DamianAPaul/726-DSSI/726-DSSI_Images/Back.png

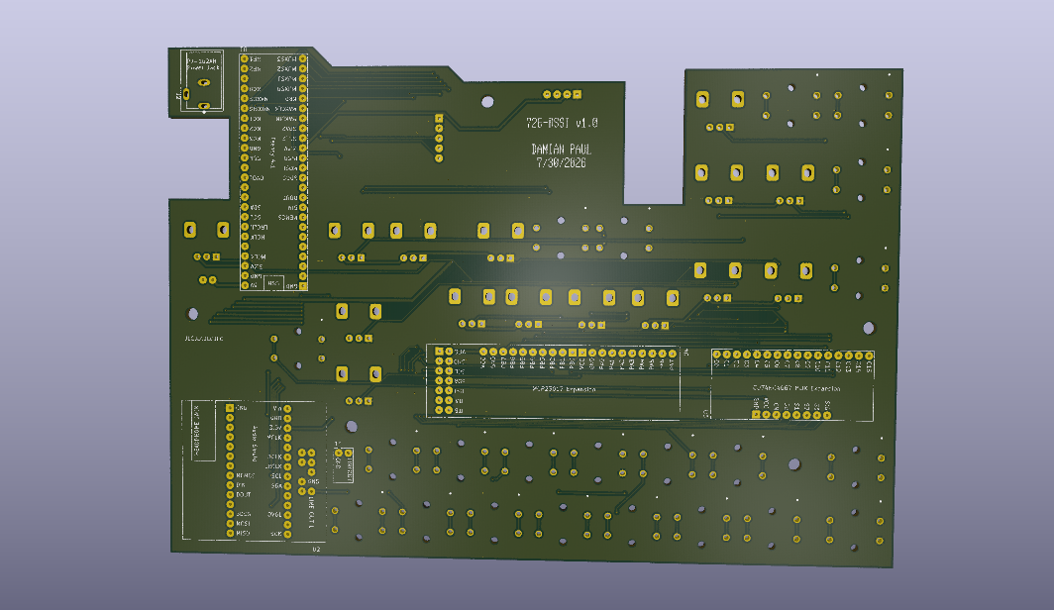
726-DSSI_Images/Back.png
