DamianAPaul/726-DSSI/726-DSSI_Images/Front.png

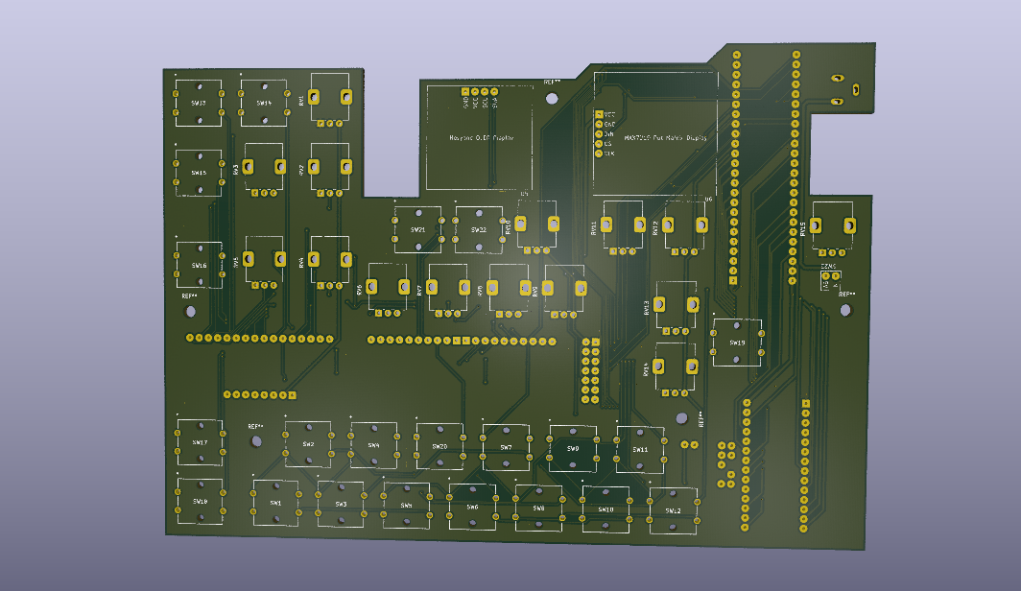
726-DSSI_Images/Front.png
