DamianAPaul/726-DSSI/726-DSSI_Images/IMG_2033_7_15_26.jpeg

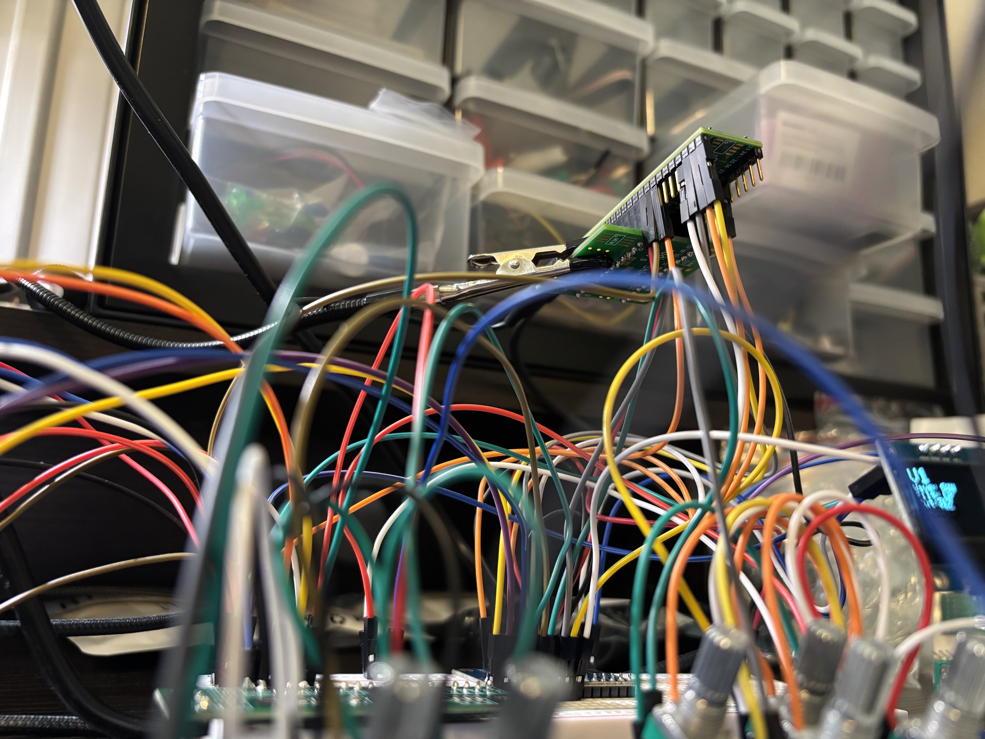
726-DSSI_Images/IMG_2033_7_15_26.jpeg
