DamianAPaul/726-DSSI/726-DSSI_Images/IMG_2102_7_22_26.jpeg

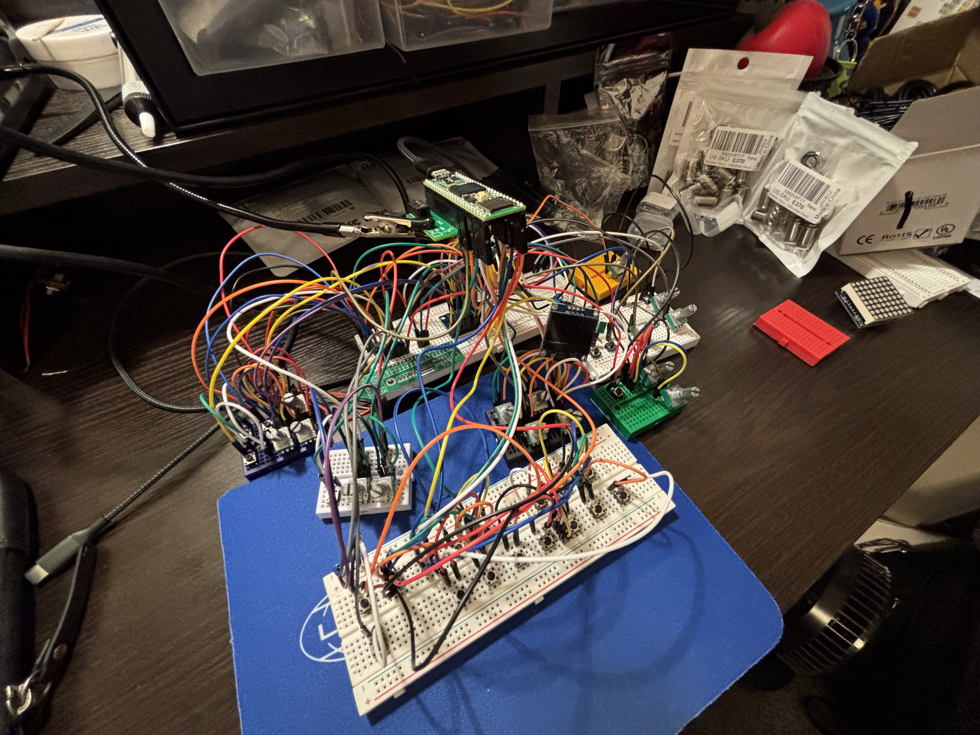
726-DSSI_Images/IMG_2102_7_22_26.jpeg
