DamianAPaul/726-DSSI/726-DSSI_Images/Screenshot 2026-07-22 at 4.46.47 PM.png

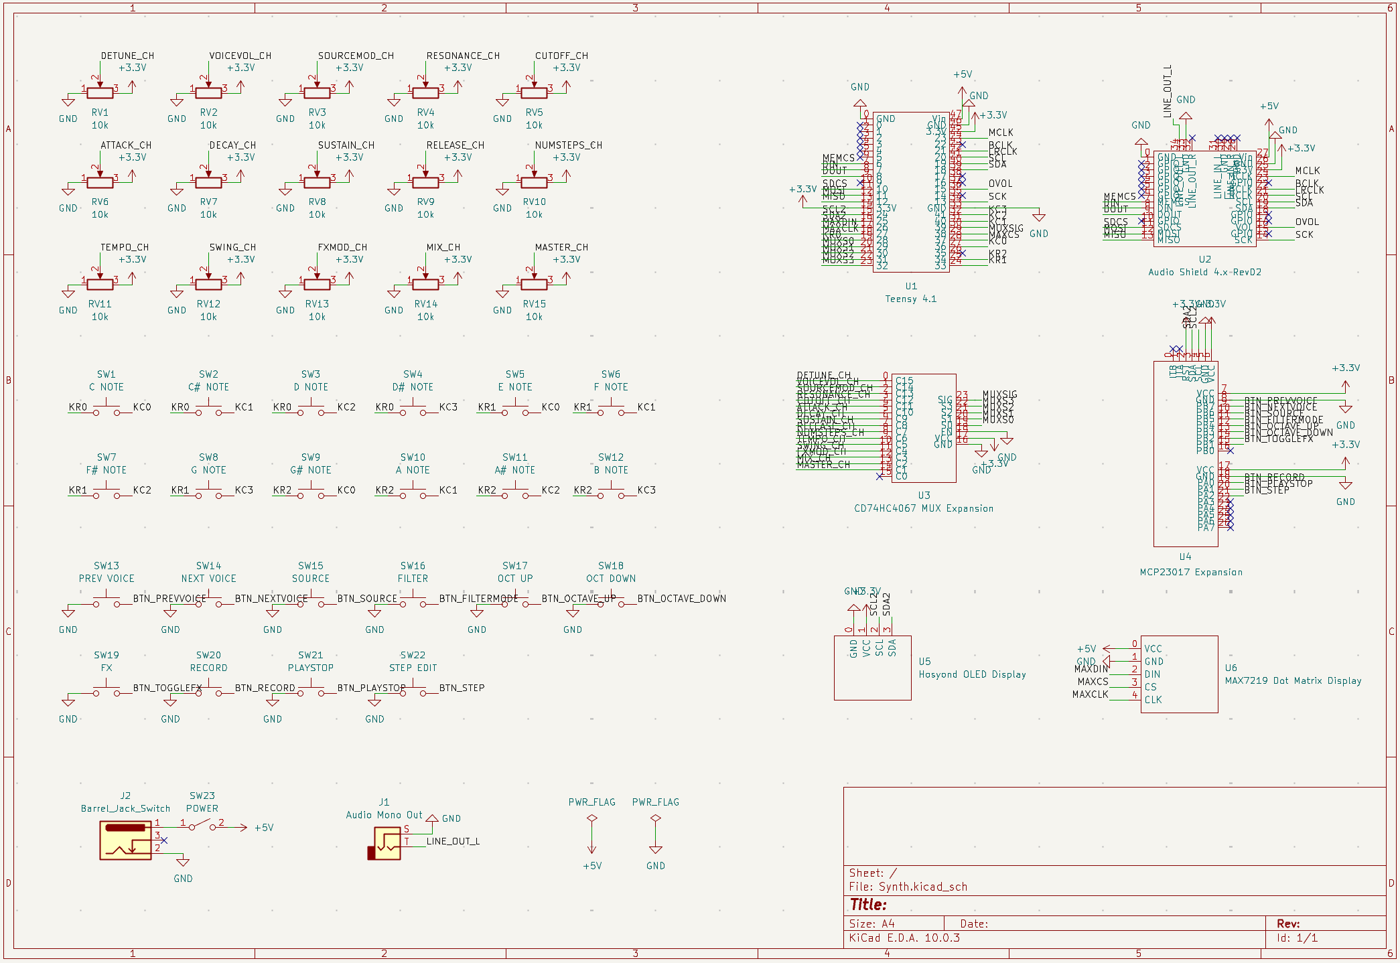
726-DSSI_Images/Screenshot 2026-07-22 at 4.46.47 PM.png
