DamianAPaul/726-DSSI/726-DSSI_Images/Screenshot 2026-07-30 at 5.10.47 PM.png

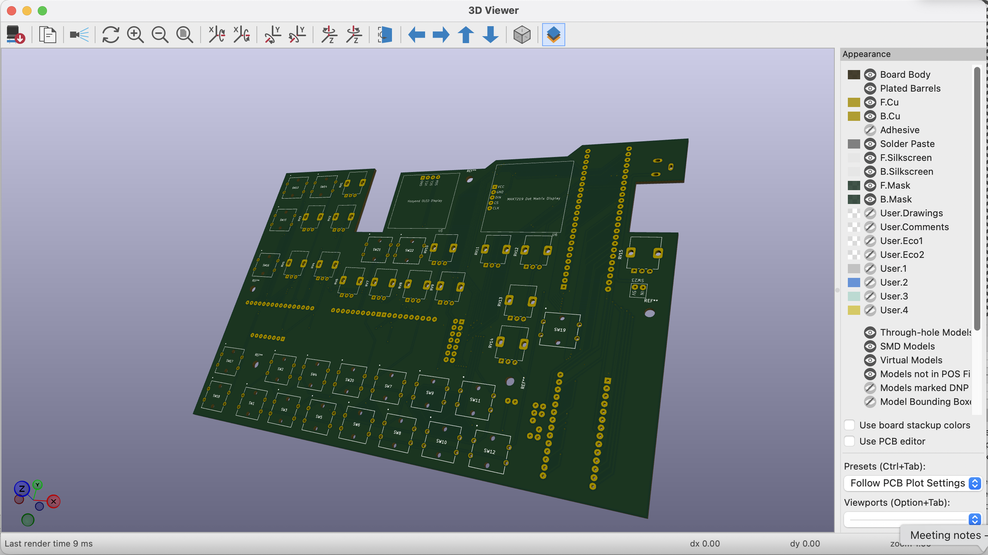
726-DSSI_Images/Screenshot 2026-07-30 at 5.10.47 PM.png
