DamianAPaul/726-DSSI/726-DSSI_Images/Screenshot 2026-07-30 at 12.36.37 PM.png

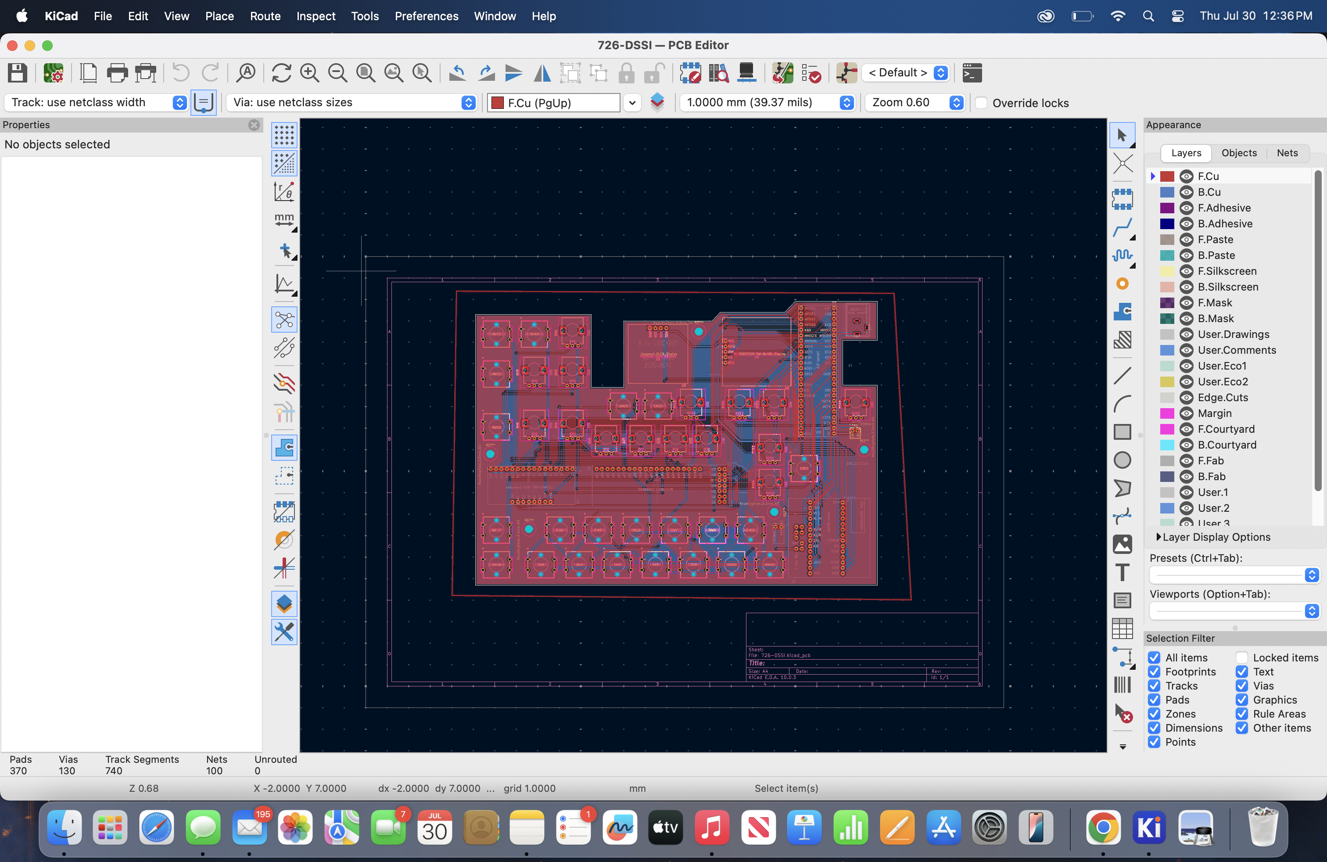
726-DSSI_Images/Screenshot 2026-07-30 at 12.36.37 PM.png
