DamianAPaul/726-DSSI/726-DSSI_Images/Screenshot 2026-08-05 at 1.29.30 PM.png

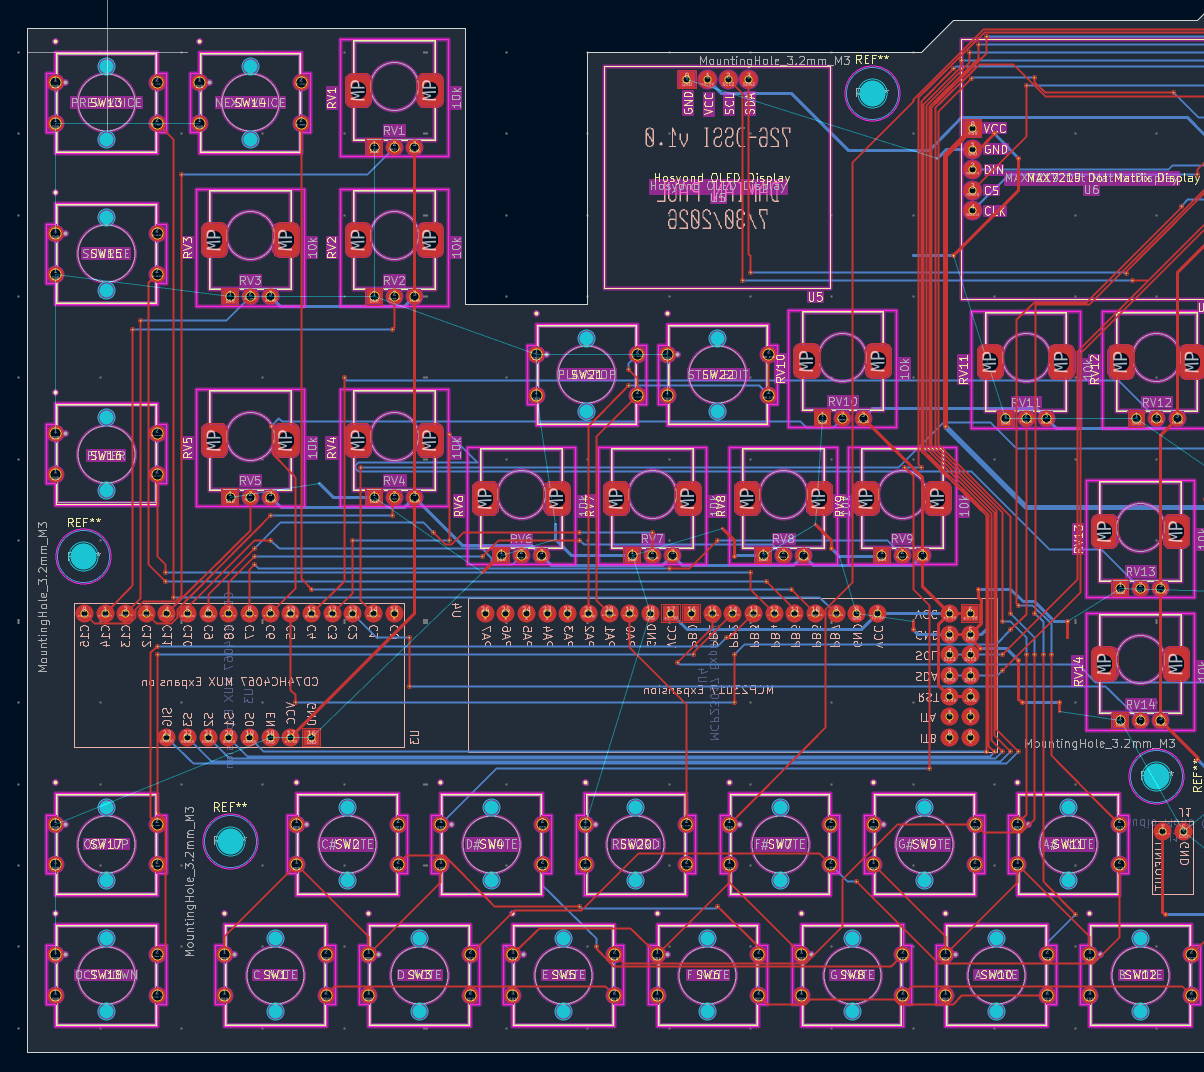
726-DSSI_Images/Screenshot 2026-08-05 at 1.29.30 PM.png
