DamianAPaul/726-DSSI/726-DSSI_Firmware/AudioObjects.h

#pragma once

#include <Audio.h>

//
// ---------- Audio Objects ----------
//

extern AudioSynthWaveform waveform1;
extern AudioSynthWaveform waveform2;
extern AudioSynthWaveform waveform3;
extern AudioSynthWaveform waveform4;
extern AudioSynthWaveform waveform5;
extern AudioSynthWaveform waveform6;
extern AudioSynthWaveform waveform7;
extern AudioSynthWaveform waveform8;

extern AudioFilterStateVariable filter1;
extern AudioFilterStateVariable filter2;
extern AudioFilterStateVariable filter3;
extern AudioFilterStateVariable filter4;
extern AudioFilterStateVariable filter5;
extern AudioFilterStateVariable filter6;
extern AudioFilterStateVariable filter7;
extern AudioFilterStateVariable filter8;
extern AudioFilterStateVariable filter9;
extern AudioFilterStateVariable filter10;
extern AudioFilterStateVariable filter11;
extern AudioFilterStateVariable filter12;
extern AudioFilterStateVariable filter13;
extern AudioFilterStateVariable filter14;
extern AudioFilterStateVariable filter15;
extern AudioFilterStateVariable filter16;
extern AudioFilterStateVariable filter17;
extern AudioFilterStateVariable filter18;
extern AudioFilterStateVariable filter19;
extern AudioFilterStateVariable filter20;
extern AudioFilterStateVariable filter21;
extern AudioFilterStateVariable filter22;
extern AudioFilterStateVariable filter23;
extern AudioFilterStateVariable filter24;

extern AudioEffectEnvelope envelope1;
extern AudioEffectEnvelope envelope2;
extern AudioEffectEnvelope envelope3;
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
extern AudioConnection patchCord76;
extern AudioConnection patchCord77;
extern AudioConnection patchCord78;
extern AudioConnection patchCord79;
extern AudioConnection patchCord80;
extern AudioConnection patchCord81;
extern AudioConnection patchCord82;
extern AudioConnection patchCord83;
extern AudioConnection patchCord84;

//
// Audio Shield
//

extern AudioControlSGTL5000 audioShield;
